speedypleath/control-unit-kicad/docs/control-unit-circuit.png

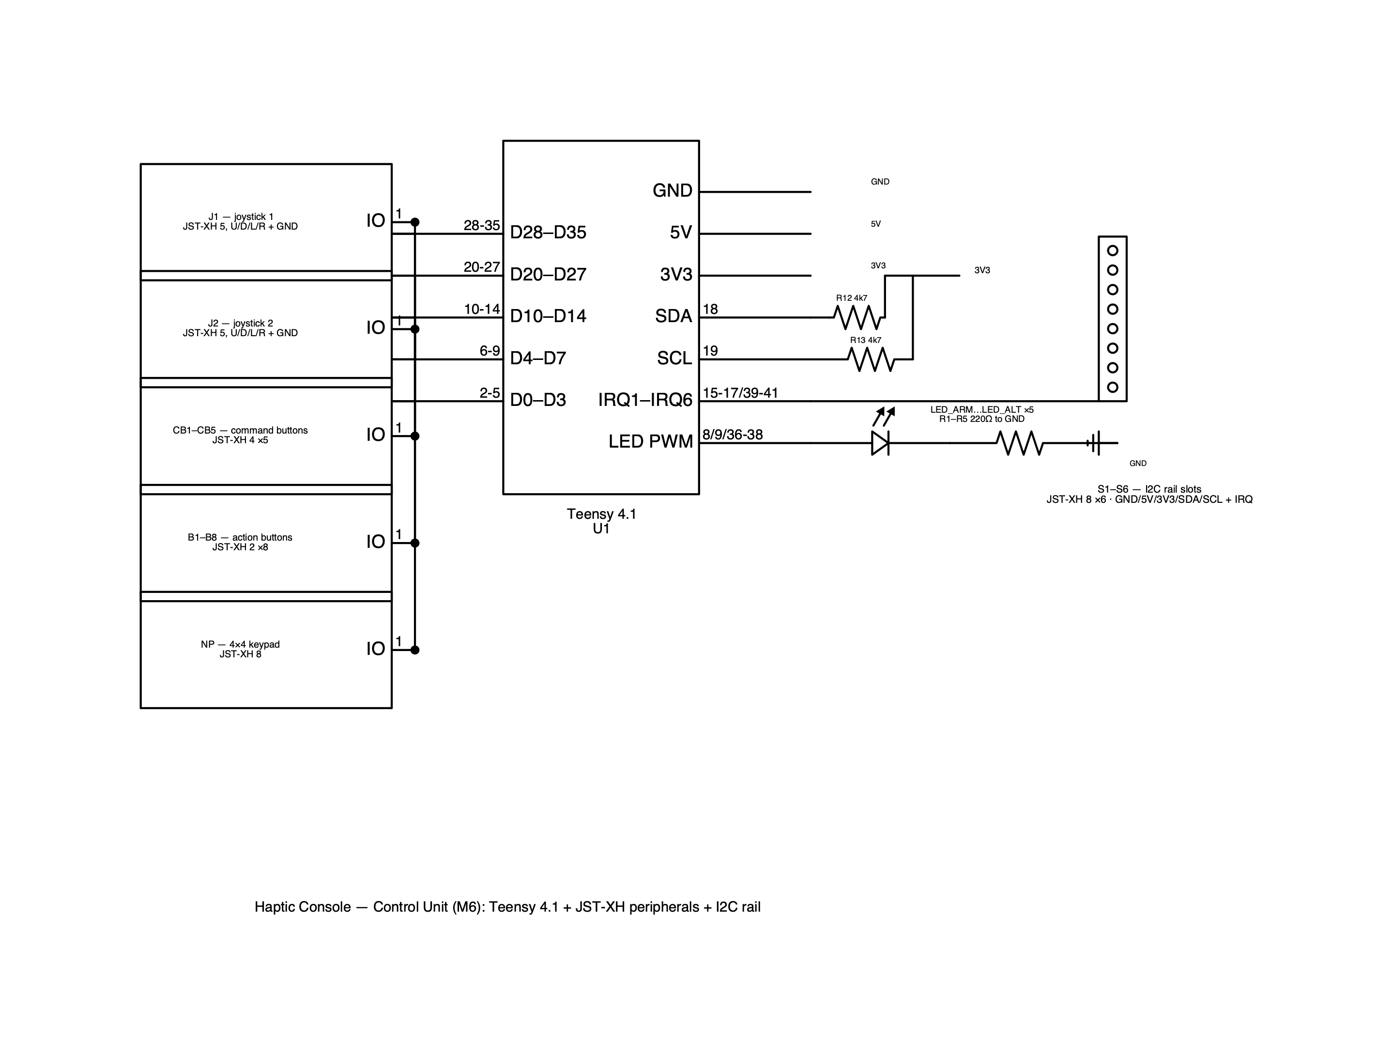
docs/control-unit-circuit.png
