speedypleath/control-unit-kicad/renders/cu_detail_buttons.png

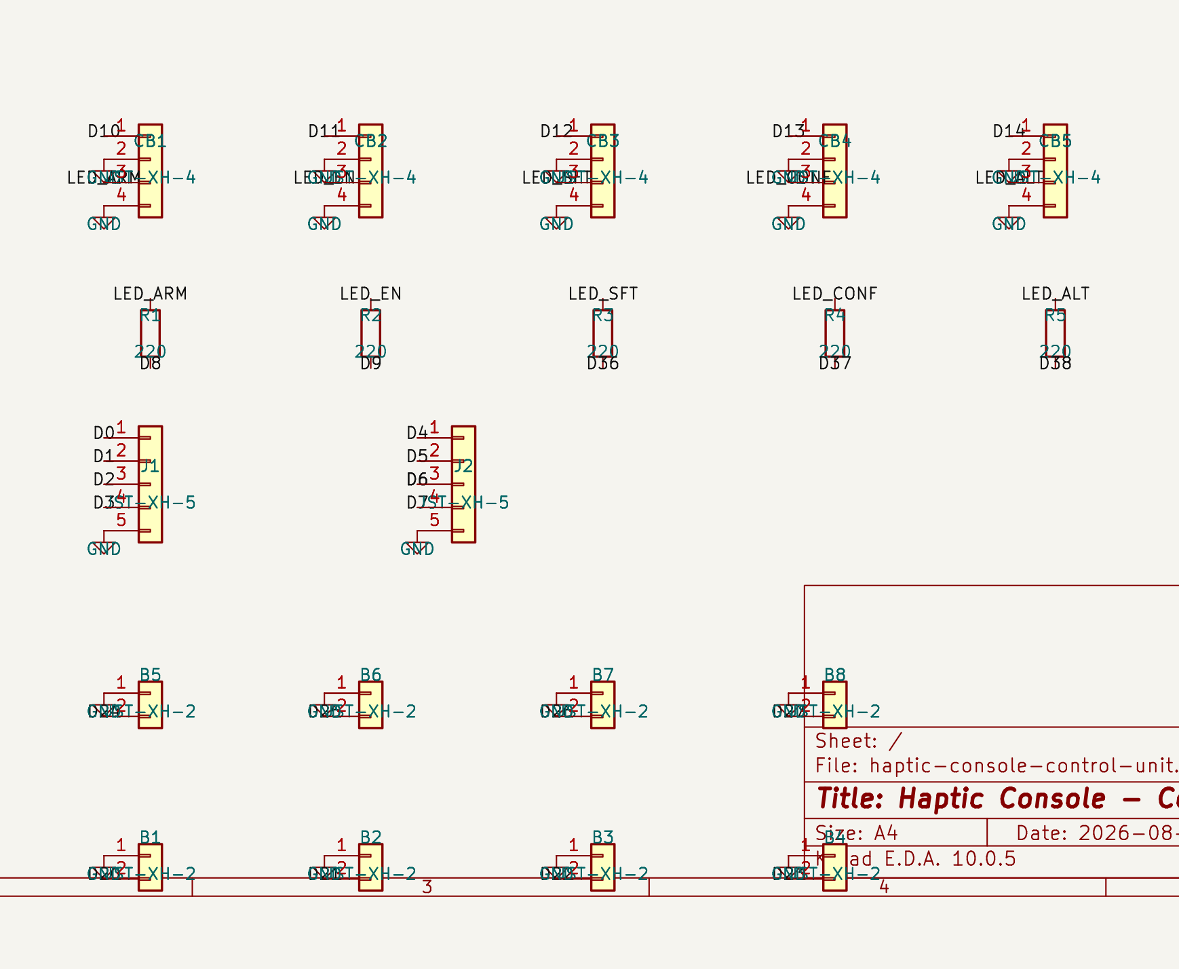
renders/cu_detail_buttons.png
