speedypleath/control-unit-kicad/renders/cu_detail_left.png

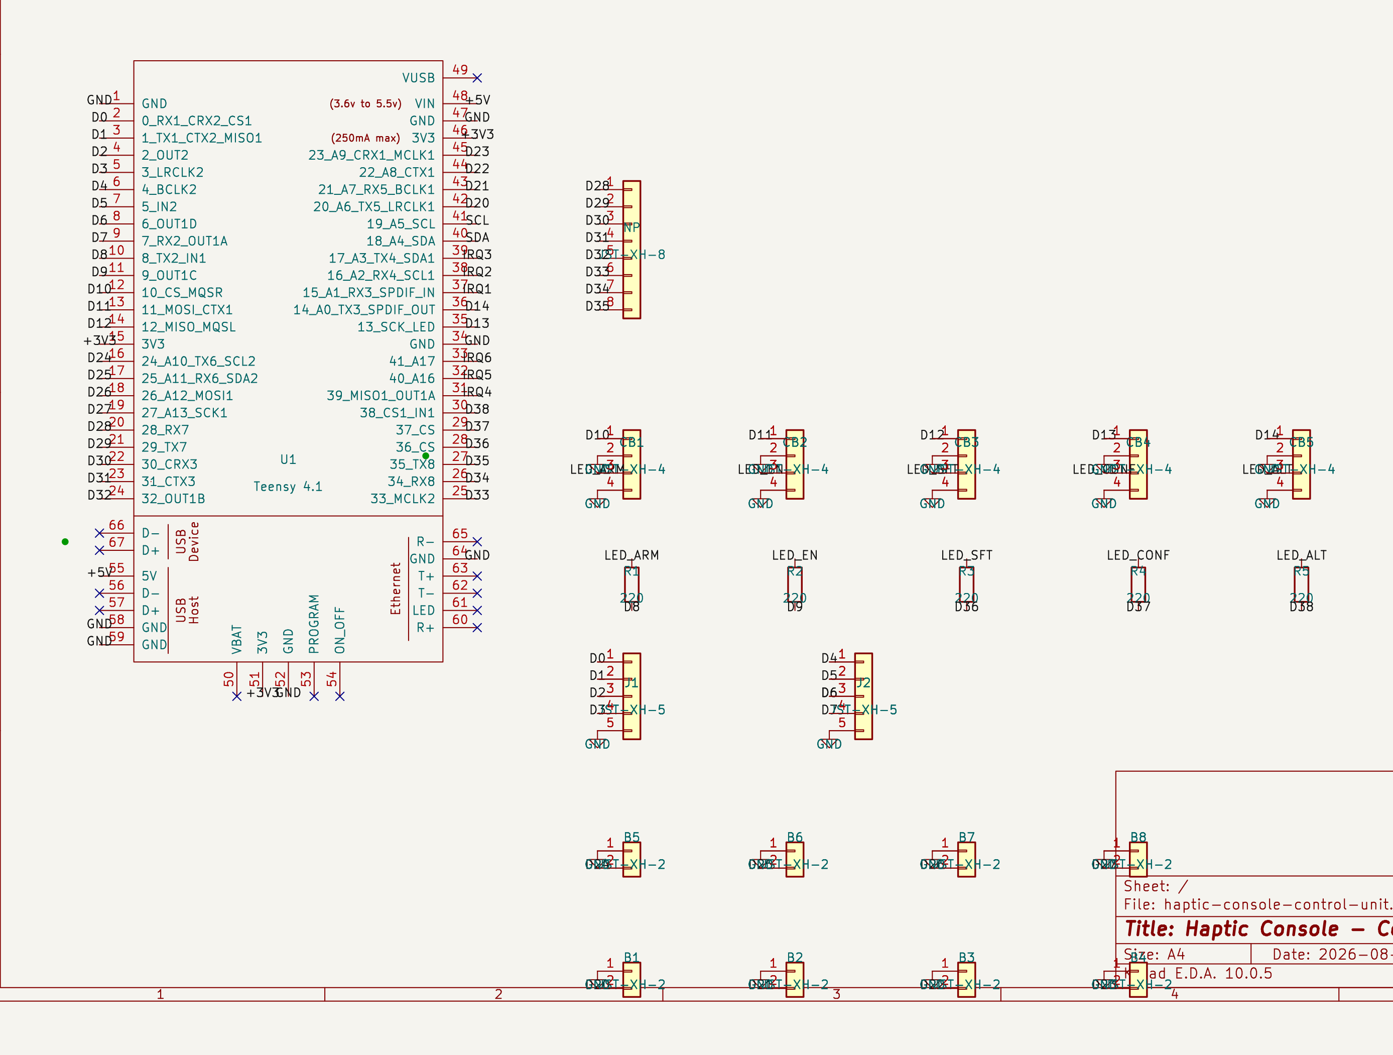
renders/cu_detail_left.png
