speedypleath/control-unit-kicad/renders/cu_detail_rails.png

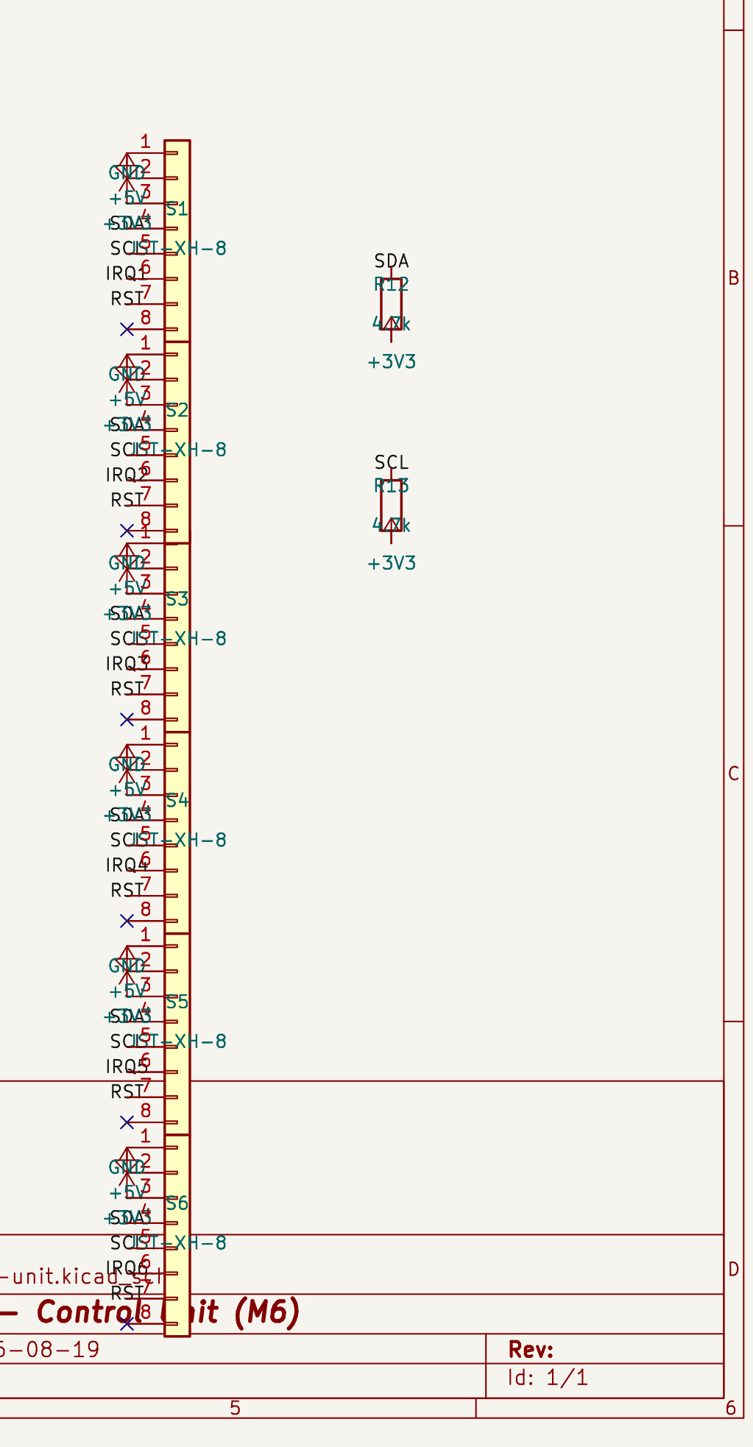
renders/cu_detail_rails.png
