speedypleath/control-unit-kicad/renders/cu_detail_teensy.png

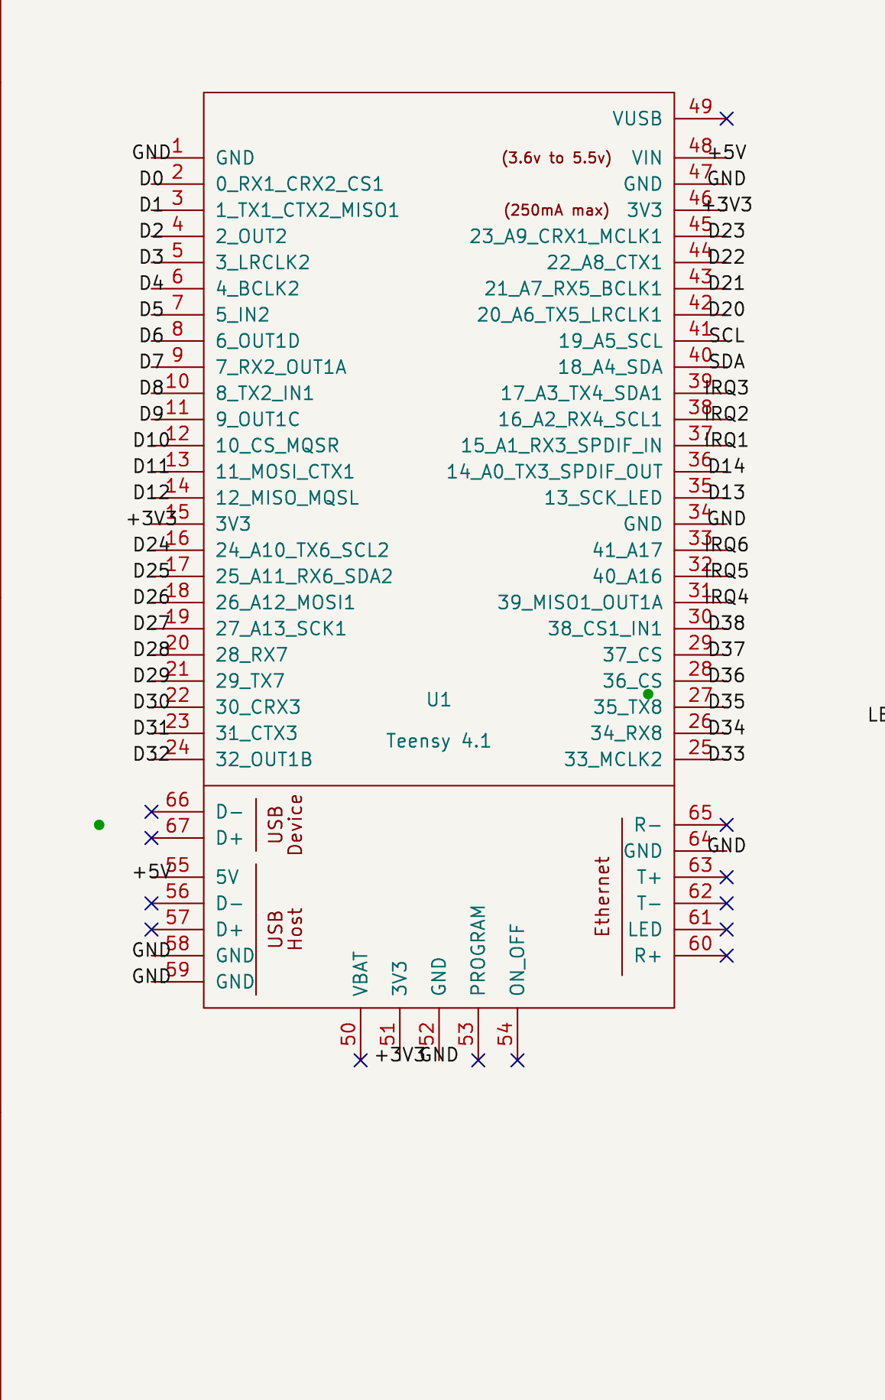
renders/cu_detail_teensy.png
