speedypleath/control-unit-kicad/renders/cu_final.png

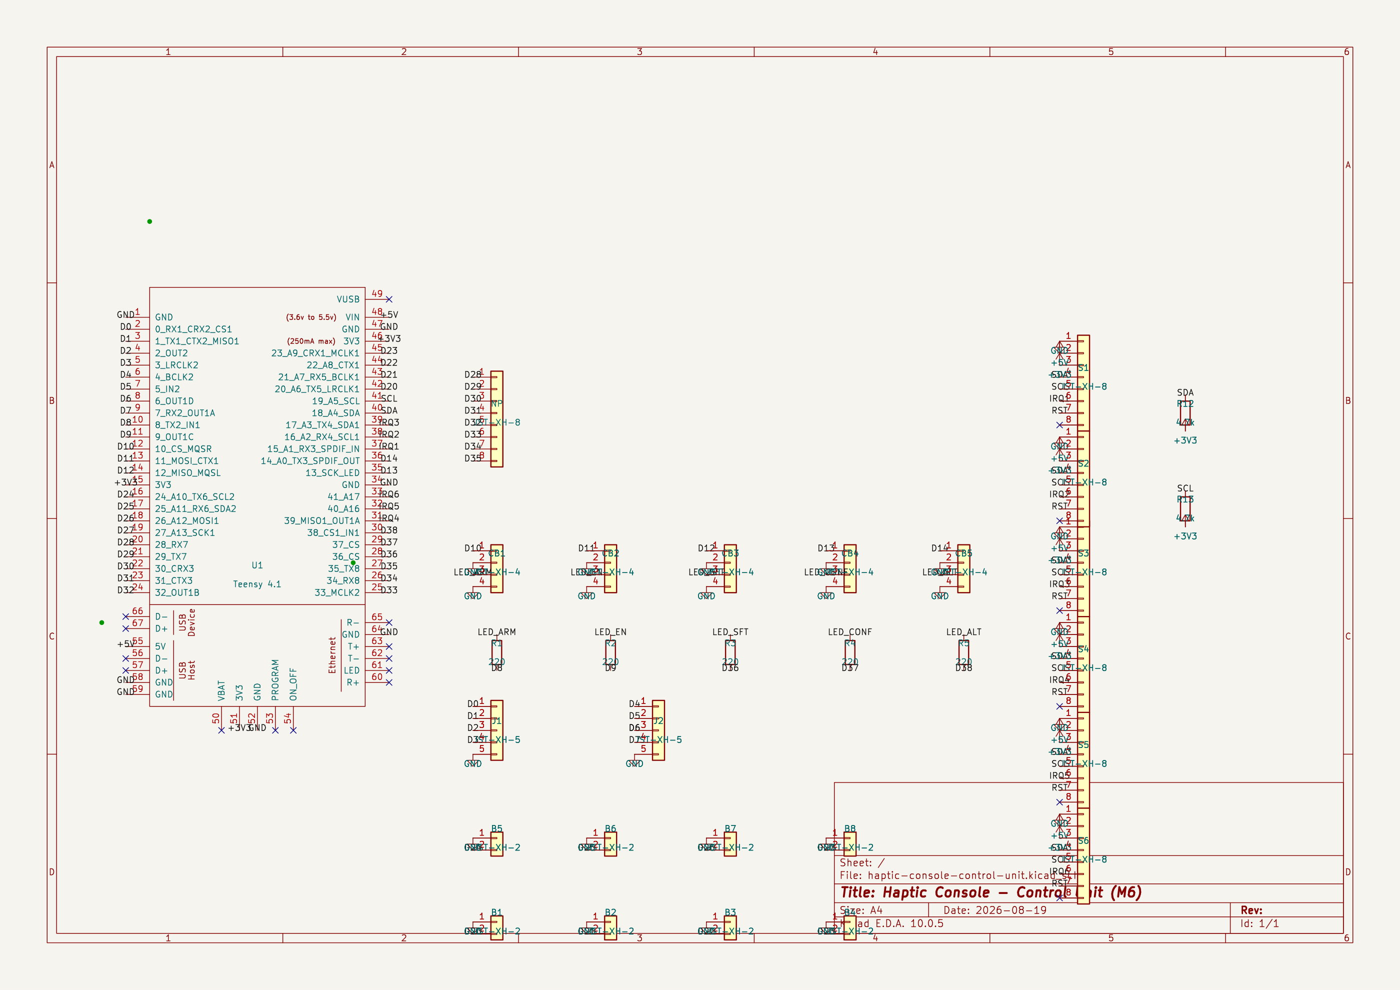
renders/cu_final.png
