speedypleath/control-unit-kicad/renders/cu_sch.png

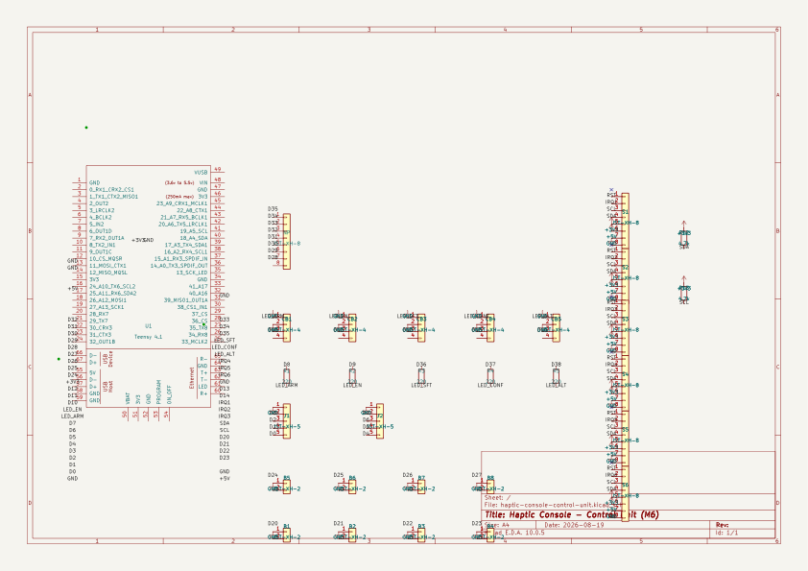
renders/cu_sch.png
