speedypleath/control-unit-kicad/renders/pcb-2d-composite-final.png

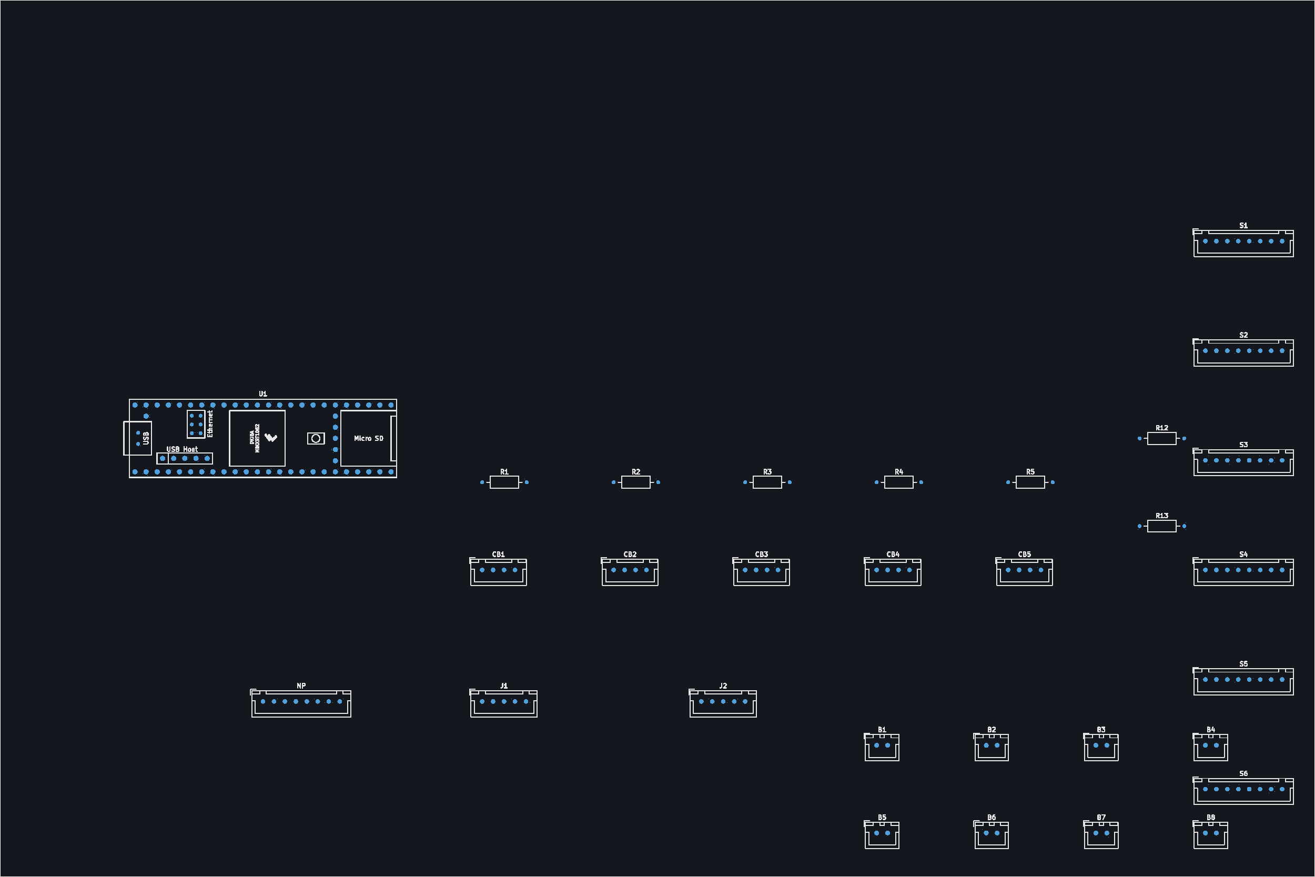
renders/pcb-2d-composite-final.png
