speedypleath/control-unit-kicad/renders/pcb-3d-top-4k-v2.png

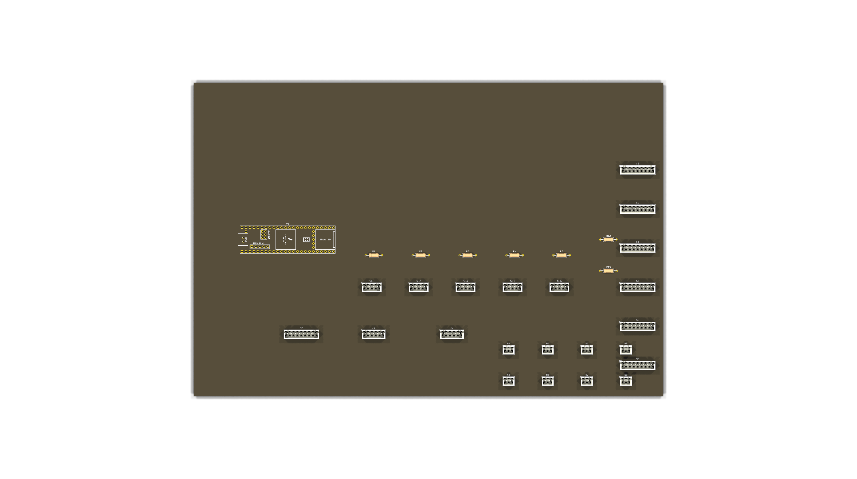
renders/pcb-3d-top-4k-v2.png
