speedypleath/control-unit-kicad/renders/pcb-3d-top-v3.png

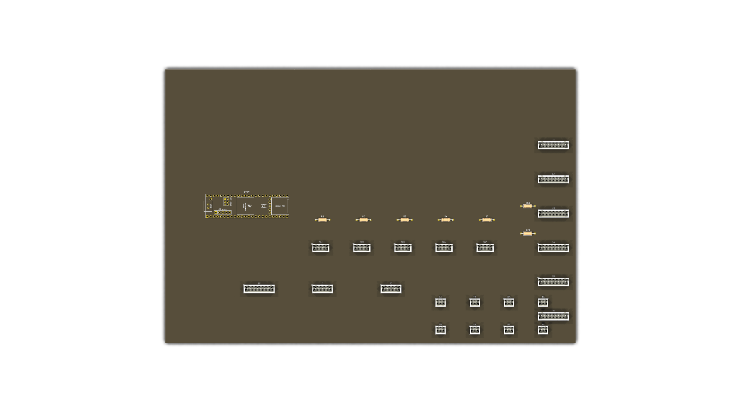
renders/pcb-3d-top-v3.png
