speedypleath/control-unit-kicad/renders/pcb_B_Cu.png

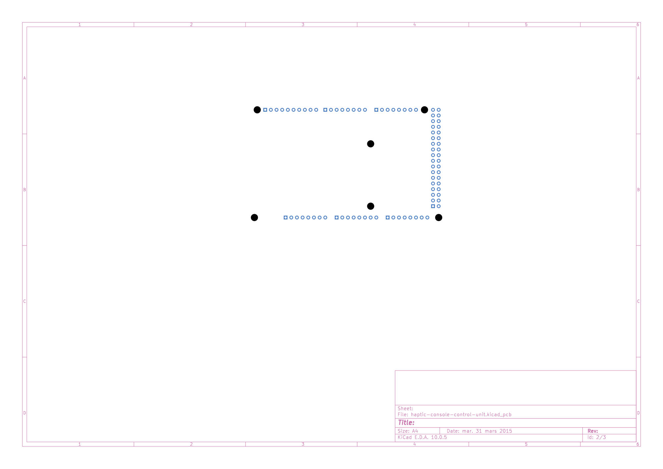
renders/pcb_B_Cu.png
