speedypleath/control-unit-kicad/renders/pcb_Edge_Cuts.png

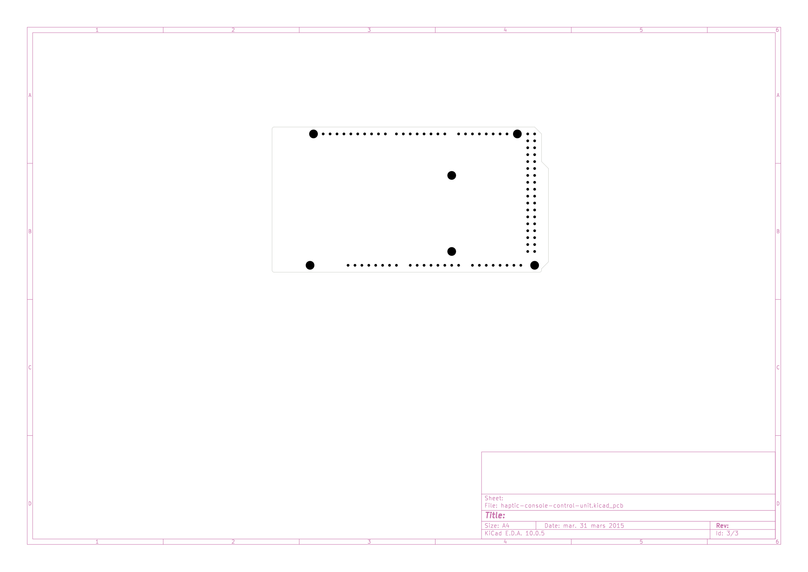
renders/pcb_Edge_Cuts.png
