speedypleath/control-unit-kicad/renders/pcb_F_Cu.png

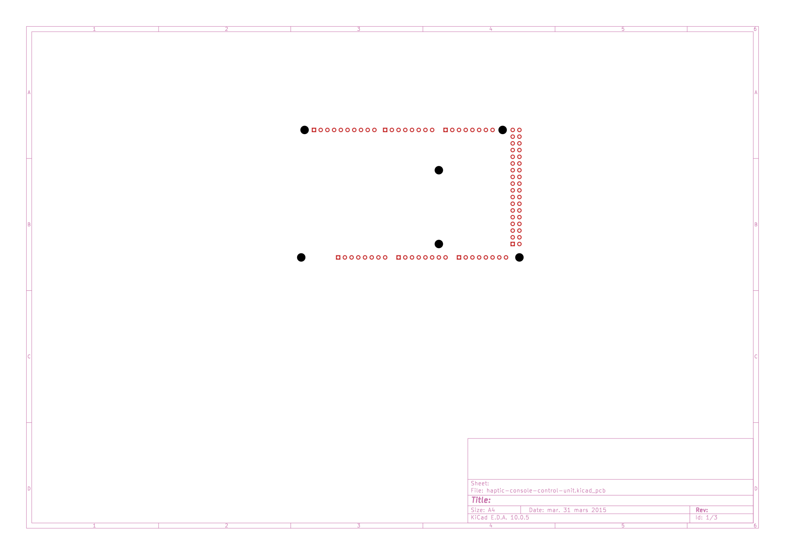
renders/pcb_F_Cu.png
