speedypleath/control-unit-kicad/renders/perfboard-wired-back.png

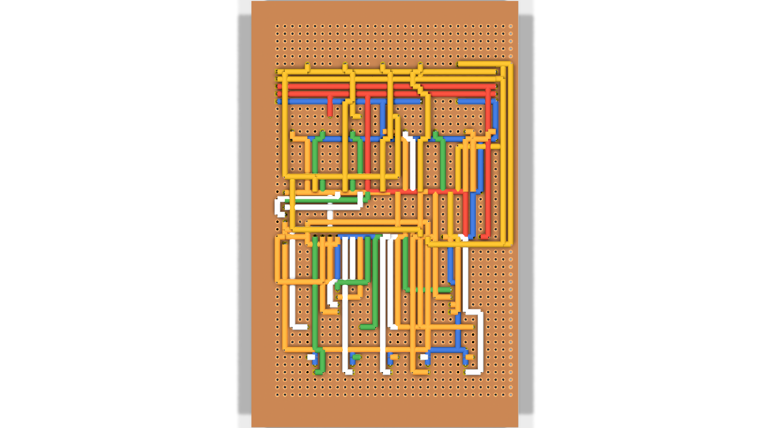
renders/perfboard-wired-back.png
