speedypleath/control-unit-kicad/renders/manufactured-board-v2-render.png

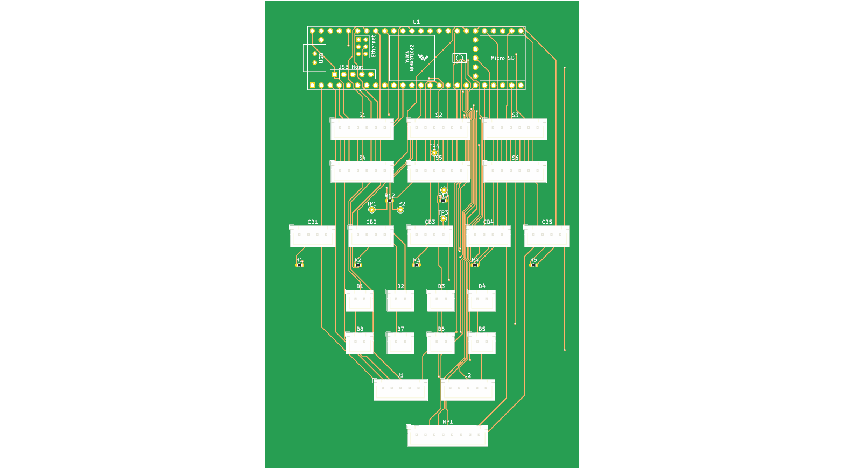
renders/manufactured-board-v2-render.png
